Alekhine23/Chess-Robot/Solidworks Model/End Effector/end effector assembly.SLDASM

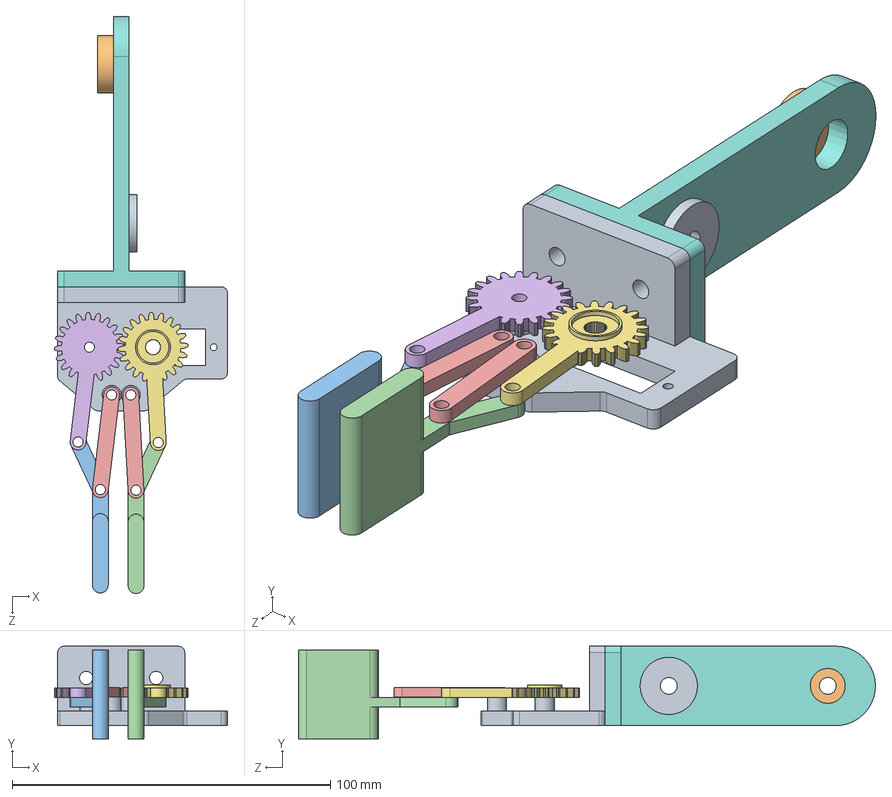
[picture p5: CAD file, 2025-10-30]
Solidworks Model/End Effector/end effector assembly.SLDASM
54.4 x 29.2 x 181.4 mm
chassis
chassis holder
splined grabber
unsplined grabber
link A x 2
link B
link C
standoff B
standoff A
