Alekhine23/Chess-Robot/Solidworks Model/End Effector/unsplined grabber.SLDPRT

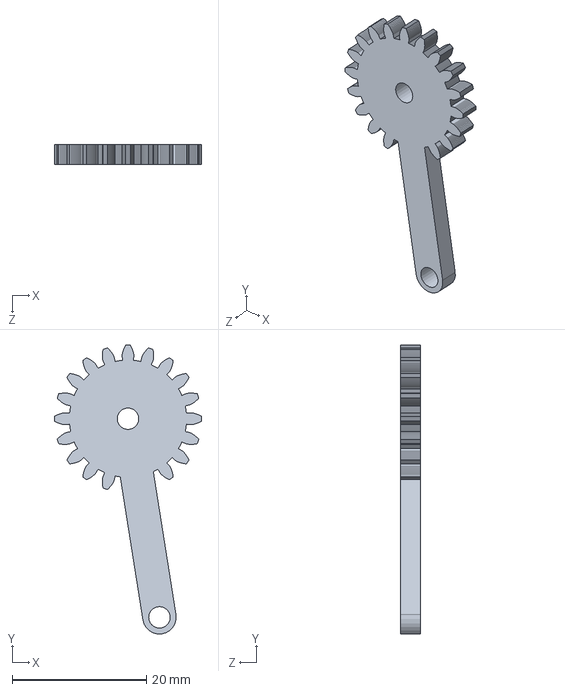
[picture p16: CAD file, 2025-10-30]
Solidworks Model/End Effector/unsplined grabber.SLDPRT
22.0 x 43.1 x 3.00 mm
