Alekhine23/Chess-Robot/STLs and dxfs/bottom base plate.DXF

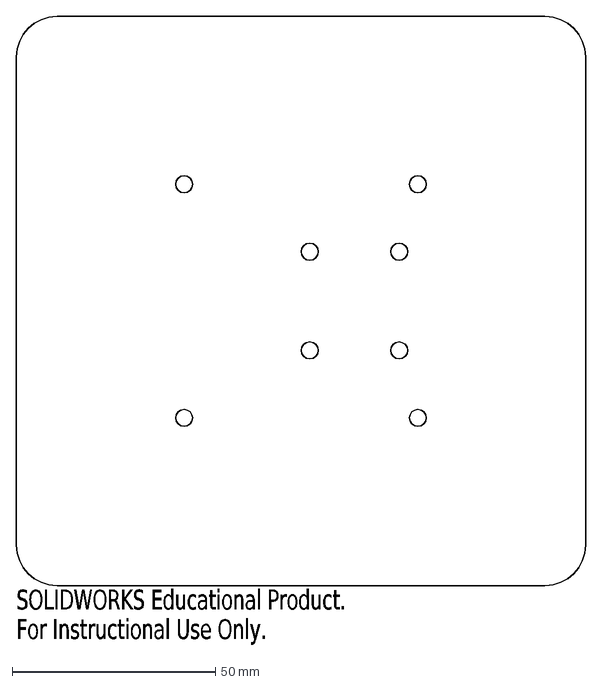
[picture p17: CAD file, 2025-10-30]
STLs and dxfs/bottom base plate.DXF
SOLIDWORKS Educational Product.
For Instructional Use Only.
