Alekhine23/Chess-Robot/Solidworks Model/End Effector/standoff A.SLDPRT

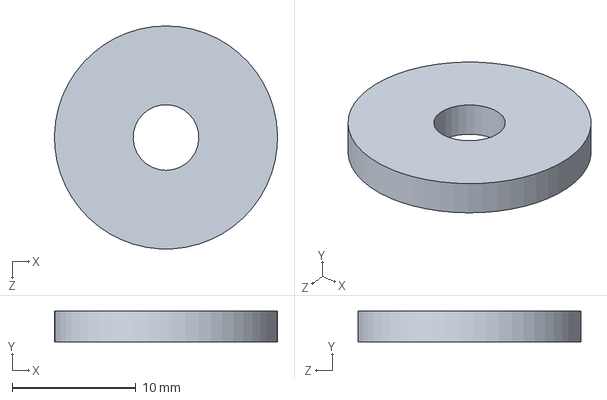
[picture p18: CAD file, 2025-10-30]
Solidworks Model/End Effector/standoff A.SLDPRT
18.0 x 2.50 x 18.0 mm
