Alekhine23/Chess-Robot/Solidworks Model/top base plate.SLDPRT

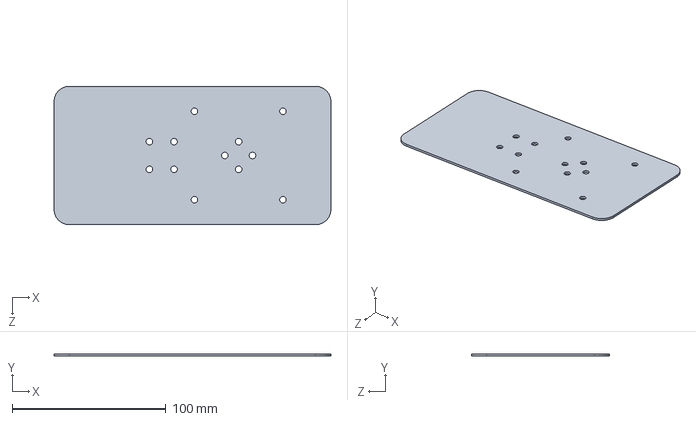
[picture p19: CAD file, 2025-10-30]
Solidworks Model/top base plate.SLDPRT
180.0 x 1.50 x 90.0 mm
