Alekhine23/Chess-Robot/STLs and dxfs/top base plate.DXF

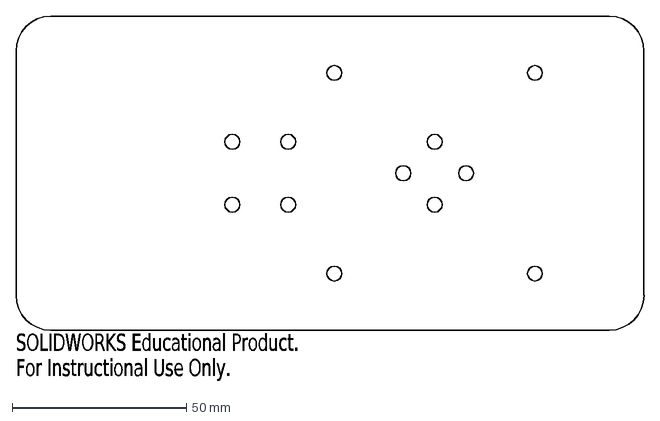
[picture p20: CAD file, 2025-10-30]
STLs and dxfs/top base plate.DXF
SOLIDWORKS Educational Product.
For Instructional Use Only.
