Alekhine23/Chess-Robot/Solidworks Model/pitch motor drive gear.SLDPRT

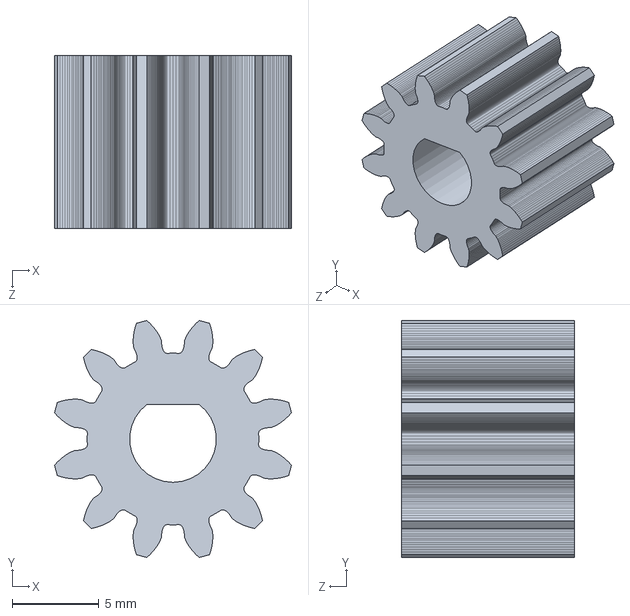
[picture p21: CAD file, 2025-10-30]
Solidworks Model/pitch motor drive gear.SLDPRT
13.7 x 13.7 x 10.0 mm
