Alekhine23/Chess-Robot/STLs and dxfs/shoulder elbow link 1A.STL

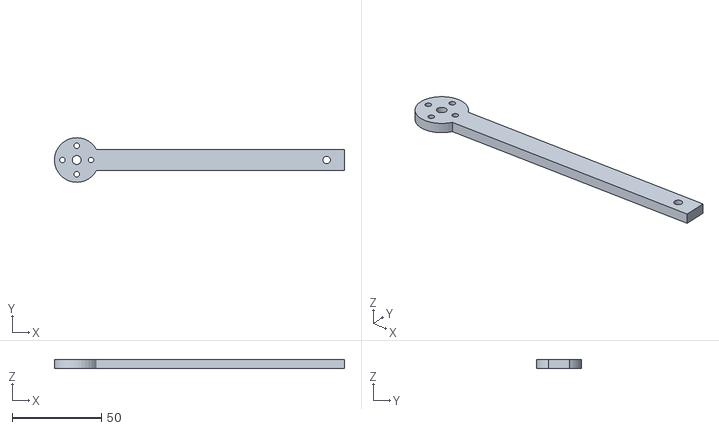
[picture p22: CAD file, 2025-10-30]
STLs and dxfs/shoulder elbow link 1A.STL
162.5 x 25.0 x 5.00
