Alekhine23/Chess-Robot/Solidworks Model/End Effector/standoff B.SLDPRT

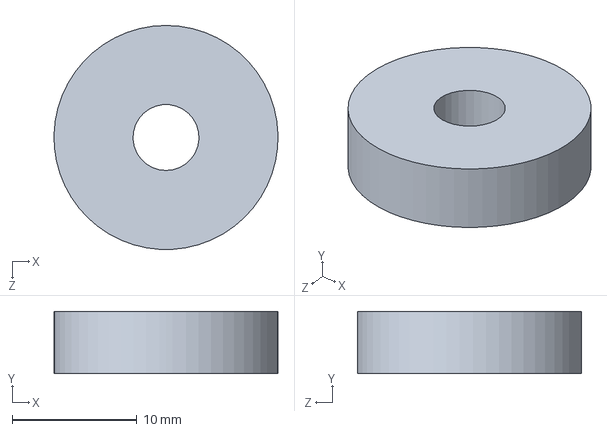
[picture p23: CAD file, 2025-10-30]
Solidworks Model/End Effector/standoff B.SLDPRT
18.0 x 5.00 x 18.0 mm
