Alekhine23/Chess-Robot/Solidworks Model/shoulder elbow link 4B.SLDPRT

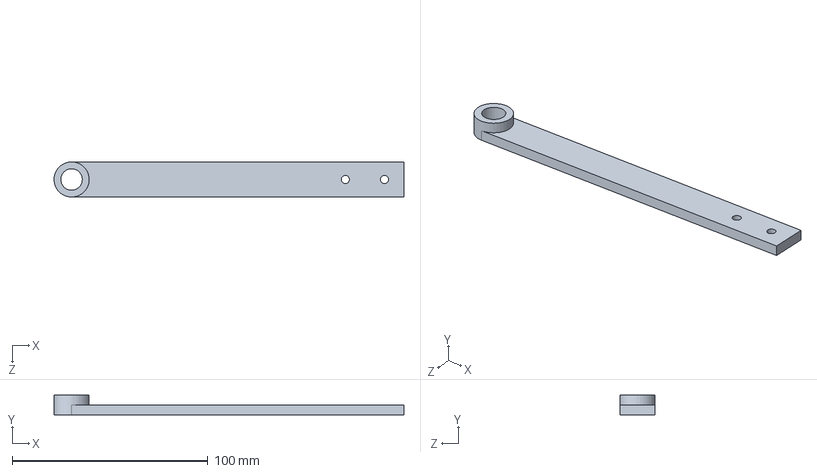
[picture p24: CAD file, 2025-10-30]
Solidworks Model/shoulder elbow link 4B.SLDPRT
179.0 x 10.0 x 18.0 mm
