Alekhine23/Chess-Robot/STLs and dxfs/shoulder elbow link 2B.STL

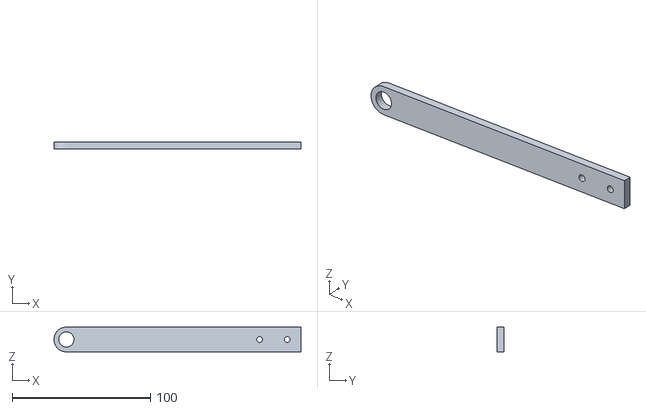
[picture p25: CAD file, 2025-10-30]
STLs and dxfs/shoulder elbow link 2B.STL
179.0 x 5.00 x 18.0
