Alekhine23/Chess-Robot/Solidworks Model/End Effector/link C.SLDPRT

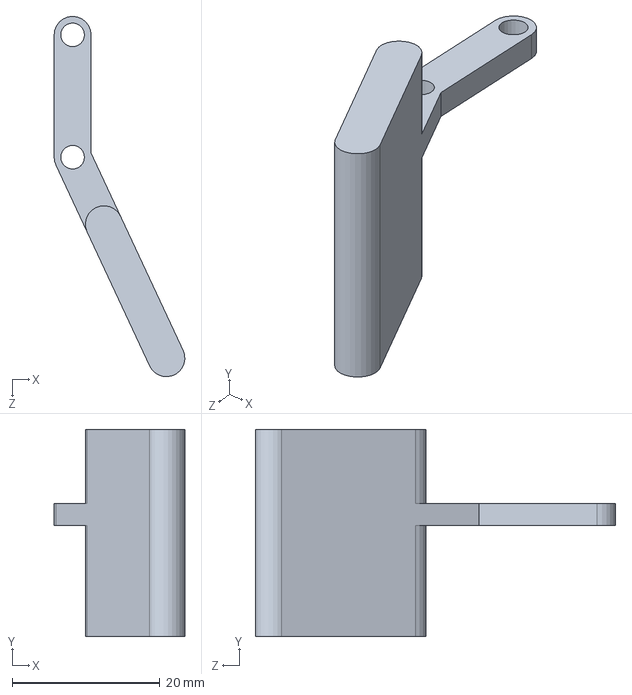
[picture p26: CAD file, 2025-10-30]
Solidworks Model/End Effector/link C.SLDPRT
17.7 x 28.0 x 48.7 mm
