Alekhine23/Chess-Robot/Solidworks Model/shoulder axle shaft collar.SLDPRT

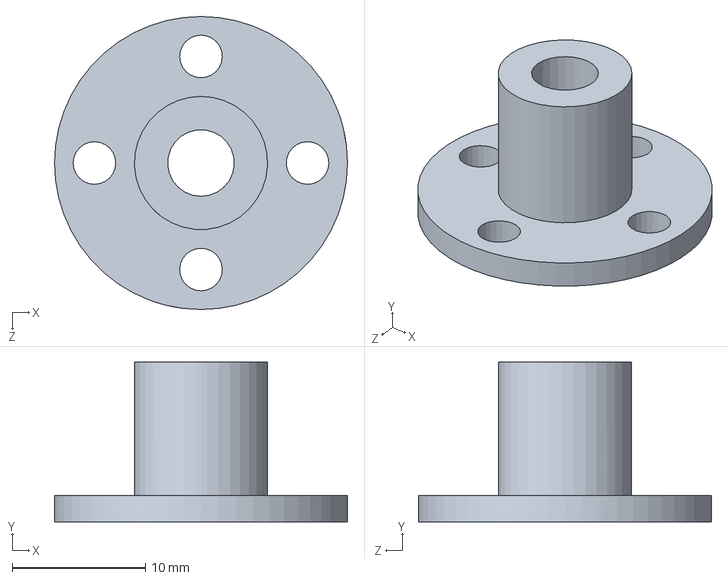
[picture p27: CAD file, 2025-10-30]
Solidworks Model/shoulder axle shaft collar.SLDPRT
22.0 x 12.0 x 22.0 mm
