Alekhine23/Chess-Robot/STLs and dxfs/chassis.STL

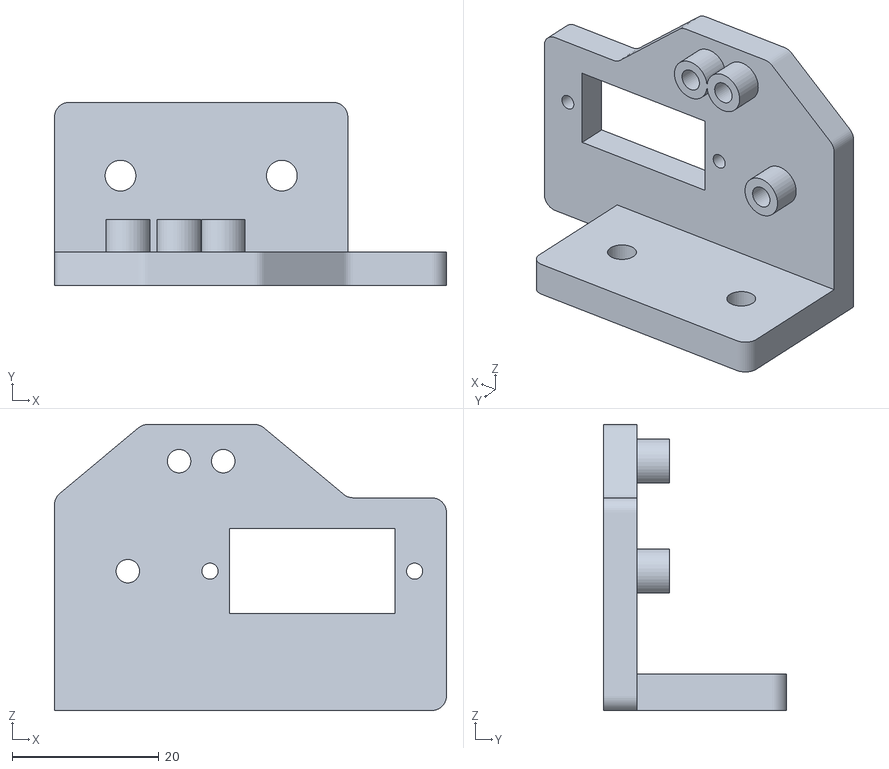
[picture p28: CAD file, 2025-10-30]
STLs and dxfs/chassis.STL
53.5 x 25.0 x 39.0
