Alekhine23/Chess-Robot/Solidworks Model/End Effector/chassis holder.SLDPRT

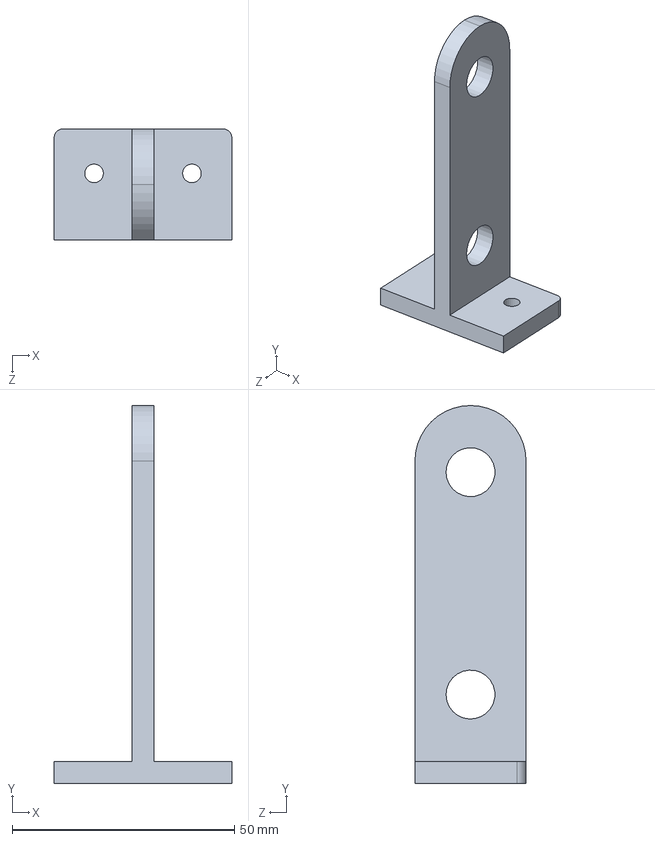
[picture p29: CAD file, 2025-10-30]
Solidworks Model/End Effector/chassis holder.SLDPRT
40.0 x 85.0 x 25.0 mm
