Alekhine23/Chess-Robot/Solidworks Model/shoulder middle axle support.SLDPRT

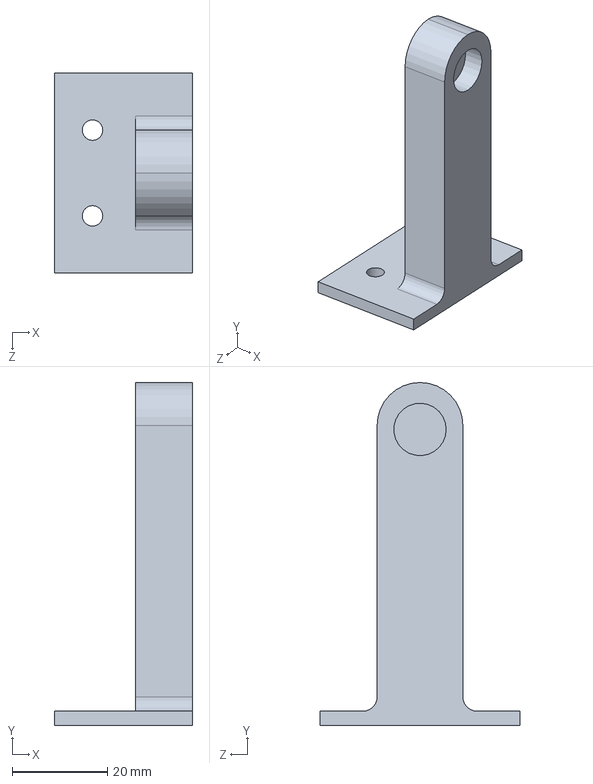
[picture p30: CAD file, 2025-10-30]
Solidworks Model/shoulder middle axle support.SLDPRT
29.0 x 72.0 x 42.0 mm
