Alekhine23/Chess-Robot/STLs and dxfs/yaw motor mount.STL

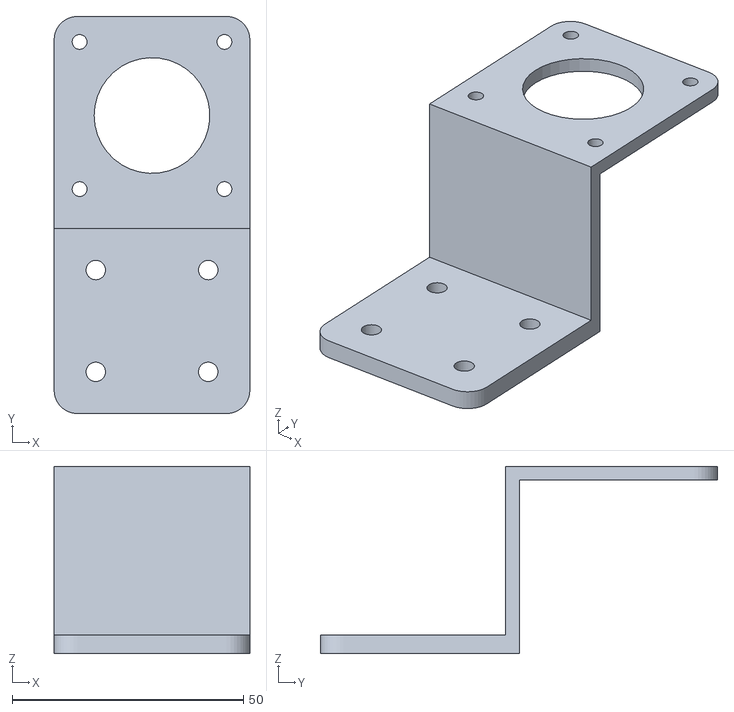
[picture p31: CAD file, 2025-10-30]
STLs and dxfs/yaw motor mount.STL
42.3 x 85.8 x 40.5
