Alekhine23/Chess-Robot/Solidworks Model/5dia 10 long shaft.SLDPRT

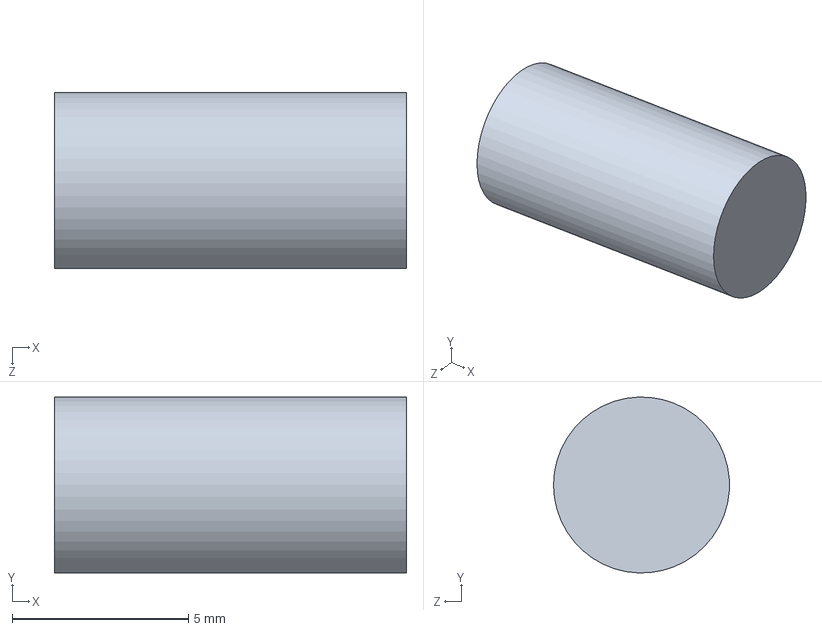
[picture p32: CAD file, 2025-10-30]
Solidworks Model/5dia 10 long shaft.SLDPRT
10.0 x 5.00 x 5.00 mm
