Alekhine23/Chess-Robot/Solidworks Model/5dia 25 long shaft.SLDPRT

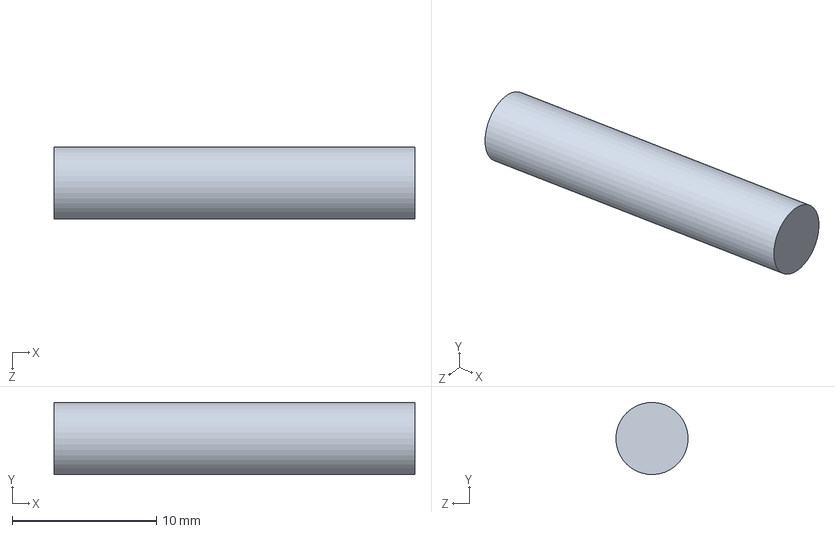
[picture p33: CAD file, 2025-10-30]
Solidworks Model/5dia 25 long shaft.SLDPRT
25.0 x 5.00 x 5.00 mm
