Alekhine23/Chess-Robot/Solidworks Model/pitch motor driven gear.SLDPRT

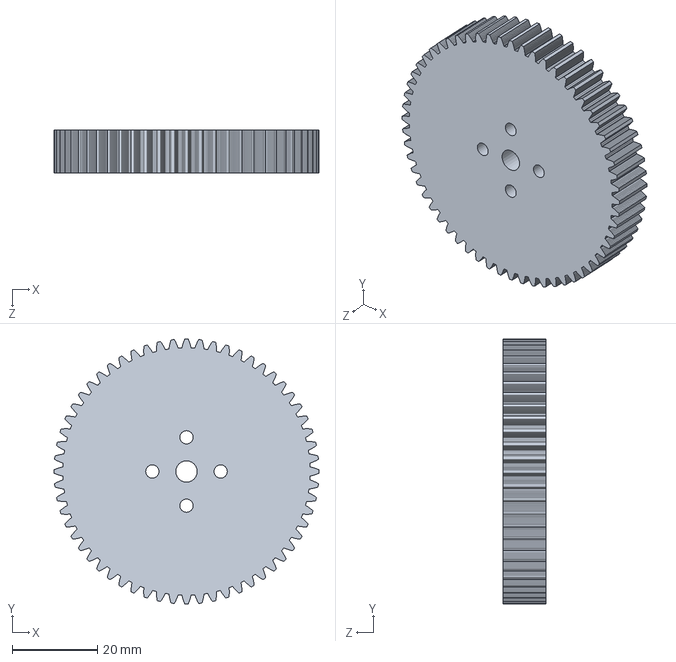
[picture p34: CAD file, 2025-10-30]
Solidworks Model/pitch motor driven gear.SLDPRT
62.0 x 62.0 x 10.0 mm
