Alekhine23/Chess-Robot/STLs and dxfs/shoulder elbow link 1B.STL

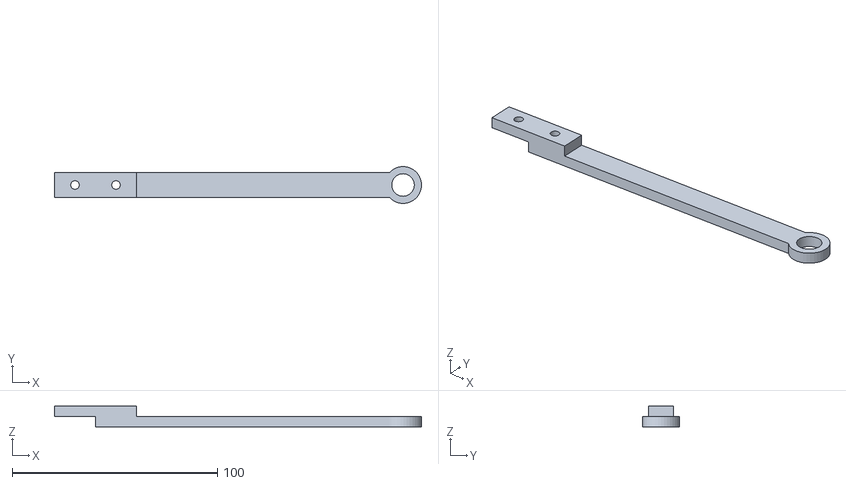
[picture p35: CAD file, 2025-10-30]
STLs and dxfs/shoulder elbow link 1B.STL
179.0 x 18.0 x 10.0
