Alekhine23/Chess-Robot/Solidworks Model/yaw motor driven gear.SLDPRT

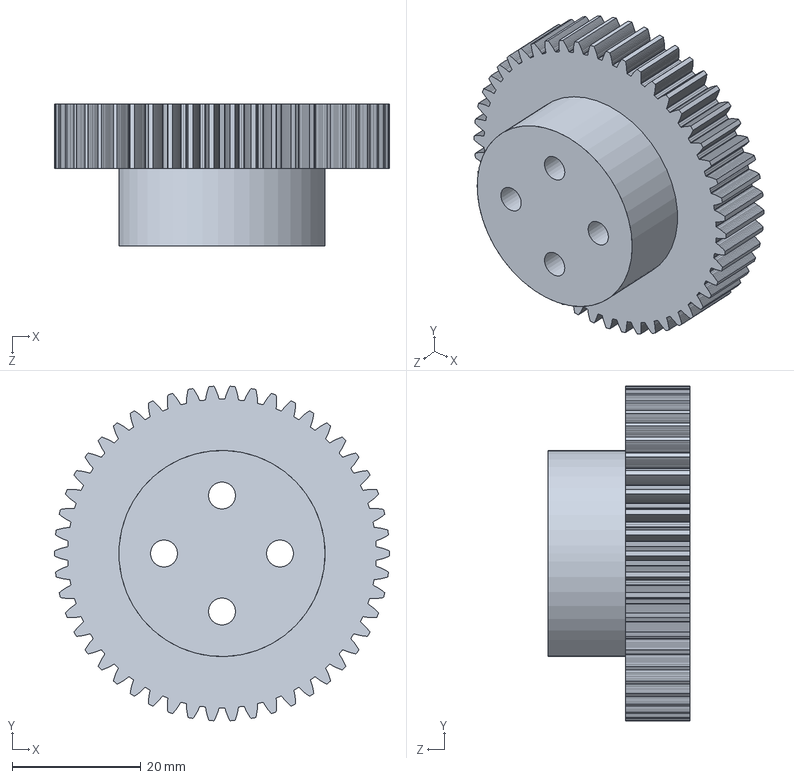
[picture p36: CAD file, 2025-10-30]
Solidworks Model/yaw motor driven gear.SLDPRT
52.0 x 51.9 x 22.0 mm
