Alekhine23/Chess-Robot/Solidworks Model/5dia 15 long shaft.SLDPRT

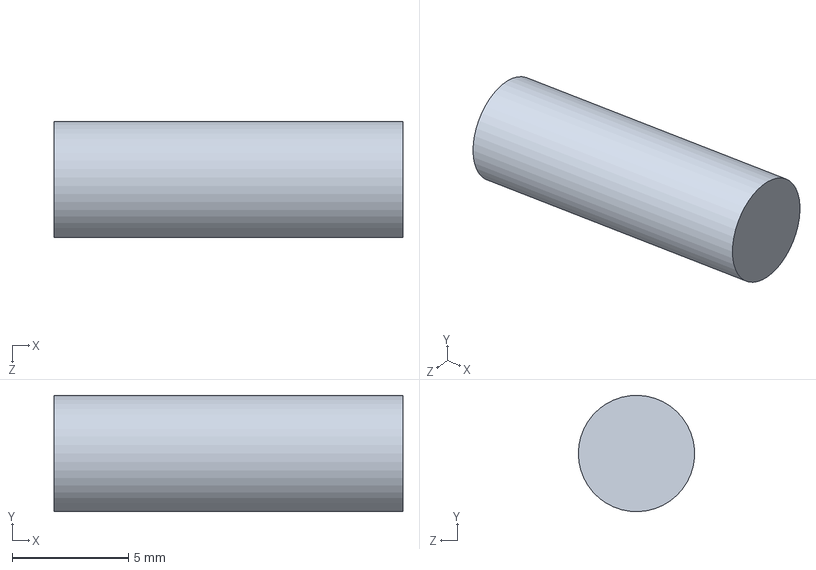
[picture p37: CAD file, 2025-10-30]
Solidworks Model/5dia 15 long shaft.SLDPRT
15.0 x 5.00 x 5.00 mm
