Alekhine23/Chess-Robot/Solidworks Model/pitch motor mount B.SLDPRT

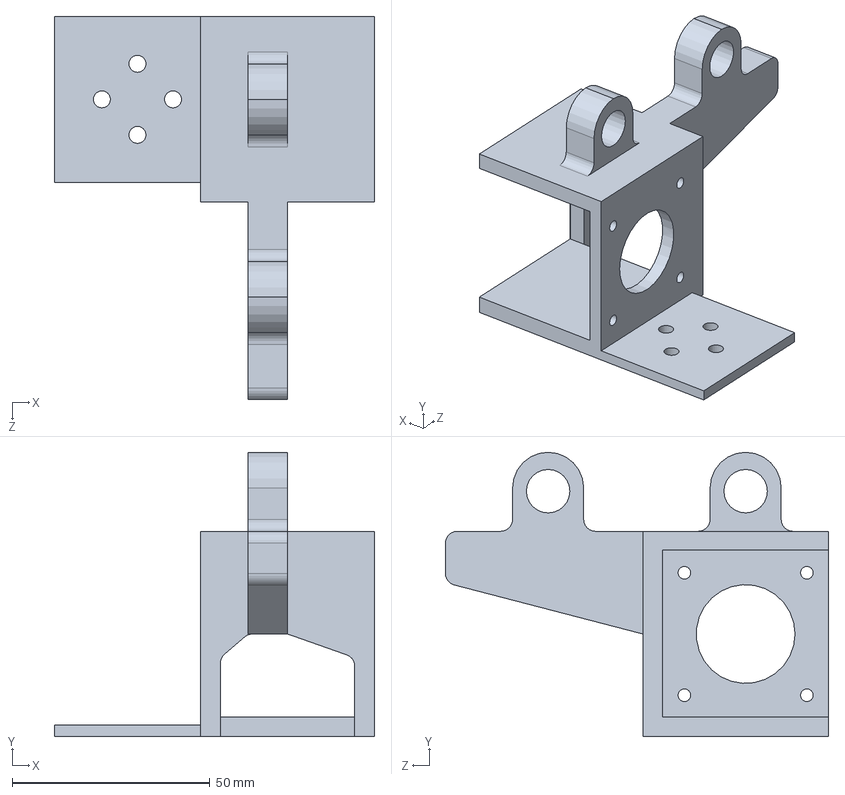
[picture p38: CAD file, 2025-10-30]
Solidworks Model/pitch motor mount B.SLDPRT
81.0 x 72.0 x 97.0 mm
