Alekhine23/Chess-Robot/STLs and dxfs/elbow triangle link.STL

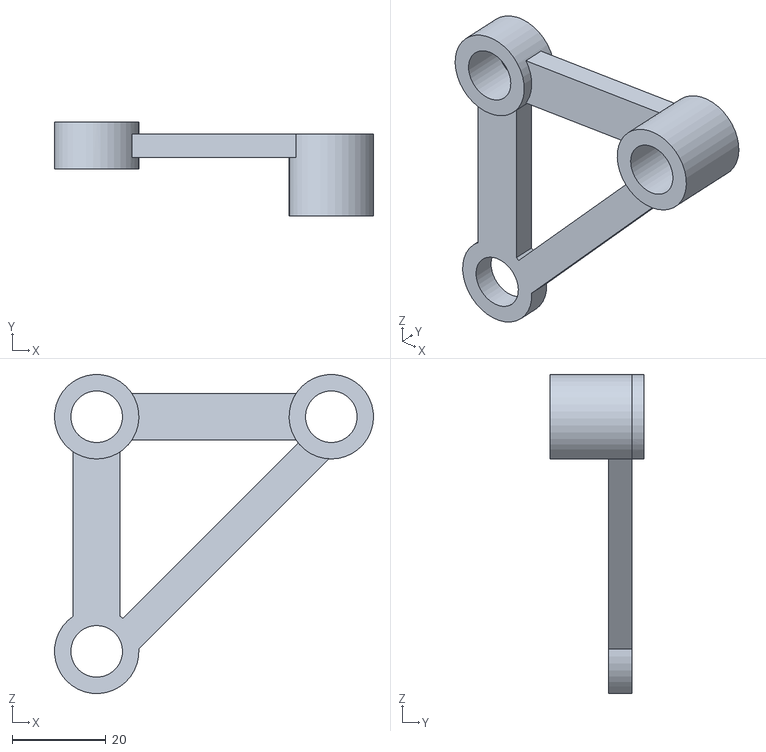
[picture p39: CAD file, 2025-10-30]
STLs and dxfs/elbow triangle link.STL
68.0 x 20.0 x 68.0
