Alekhine23/Chess-Robot/Solidworks Model/pitch motor mount A.SLDPRT

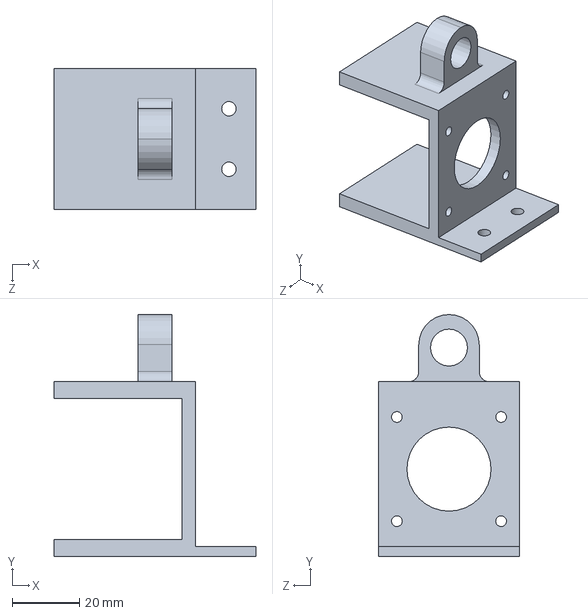
[picture p40: CAD file, 2025-10-30]
Solidworks Model/pitch motor mount A.SLDPRT
60.0 x 72.0 x 42.0 mm
