Alekhine23/Chess-Robot/Solidworks Model/5dia 20 long shaft.SLDPRT

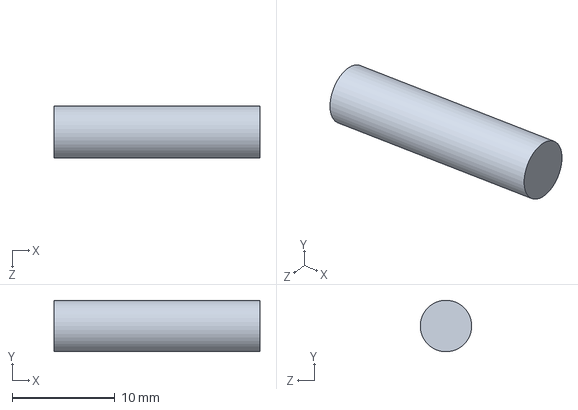
[picture p41: CAD file, 2025-10-30]
Solidworks Model/5dia 20 long shaft.SLDPRT
20.0 x 5.00 x 5.00 mm
