Alekhine23/Chess-Robot/Solidworks Model/5dia 22.5 long shaft.SLDPRT

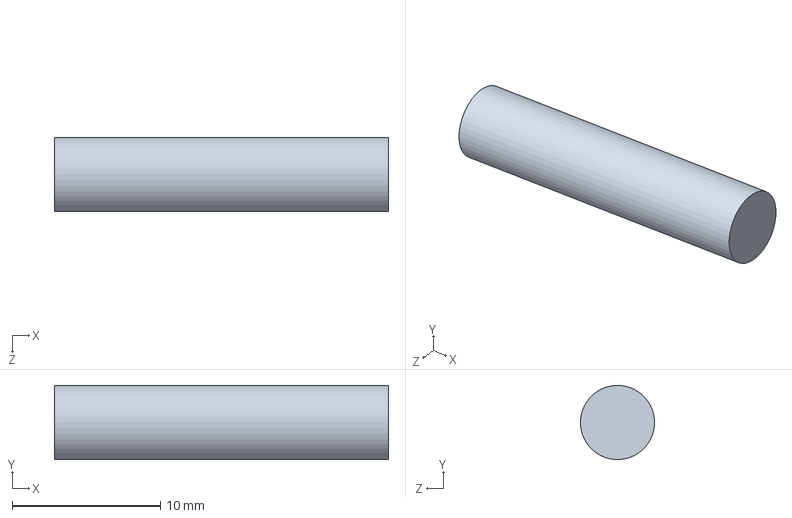
[picture p42: CAD file, 2025-10-30]
Solidworks Model/5dia 22.5 long shaft.SLDPRT
22.5 x 5.00 x 5.00 mm
