Alekhine23/Chess-Robot/Solidworks Model/board.SLDPRT

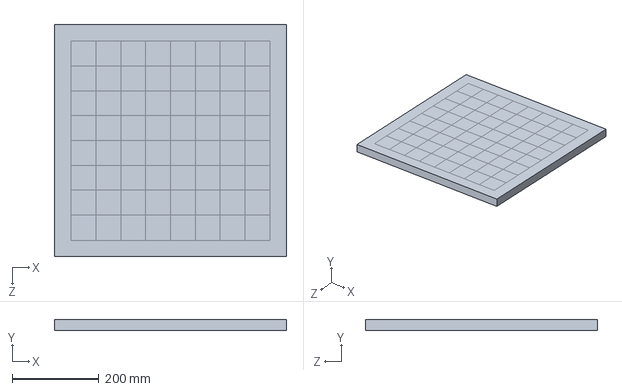
[picture p43: CAD file, 2025-10-30]
Solidworks Model/board.SLDPRT
533.4 x 25.4 x 533.4 mm
