Alekhine23/Chess-Robot/Solidworks Model/lazy susan bearing.SLDPRT

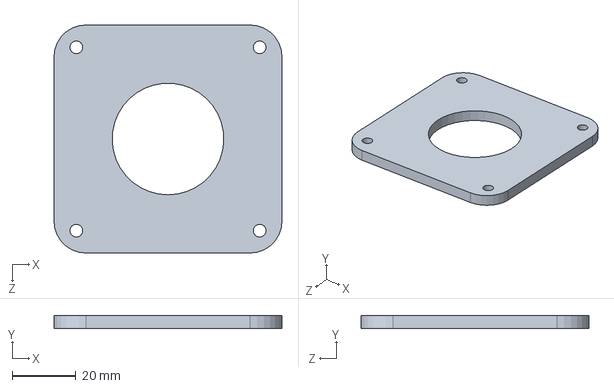
[picture p44: CAD file, 2025-10-30]
Solidworks Model/lazy susan bearing.SLDPRT
71.5 x 4.20 x 71.5 mm
