Alekhine23/Chess-Robot/Solidworks Model/base standoff.SLDPRT

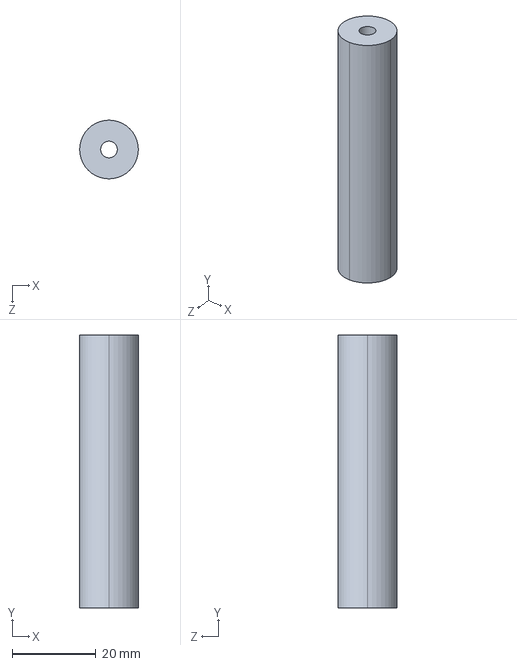
[picture p45: CAD file, 2025-10-30]
Solidworks Model/base standoff.SLDPRT
14.0 x 65.1 x 14.0 mm
