Alekhine23/Chess-Robot/Solidworks Model/5dia 59 long shaft.SLDPRT

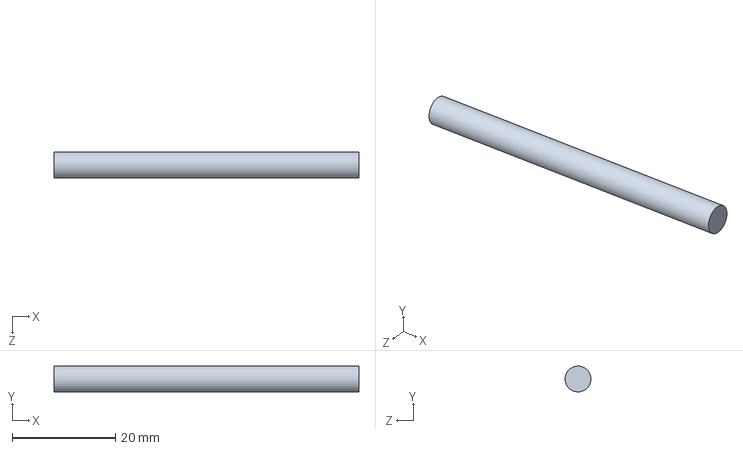
[picture p46: CAD file, 2025-10-30]
Solidworks Model/5dia 59 long shaft.SLDPRT
59.0 x 4.99 x 5.00 mm
