Alekhine23/Chess-Robot/STLs and dxfs/shoulder link 3.STL

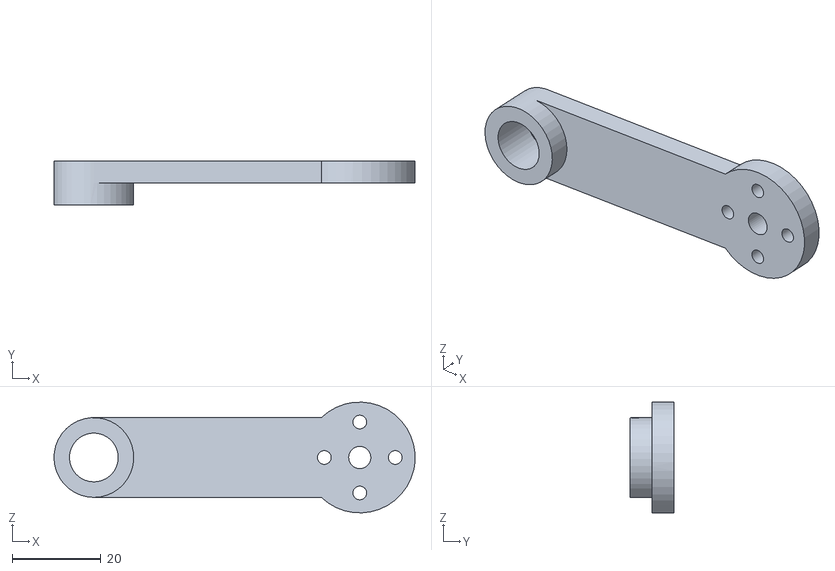
[picture p47: CAD file, 2025-10-30]
STLs and dxfs/shoulder link 3.STL
81.5 x 10.0 x 25.0
