Alekhine23/Chess-Robot/Solidworks Model/bottom base plate.SLDPRT

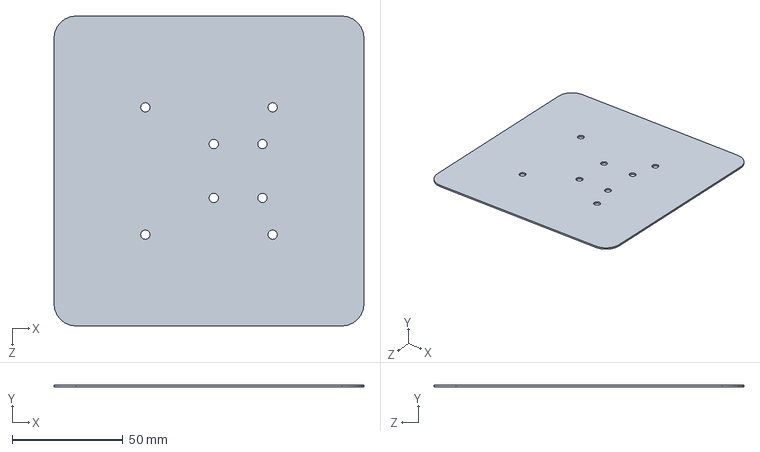
[picture p48: CAD file, 2025-10-30]
Solidworks Model/bottom base plate.SLDPRT
140.0 x 1.00 x 140.0 mm
