Alekhine23/Chess-Robot/Solidworks Model/5dia 40 long shaft.SLDPRT

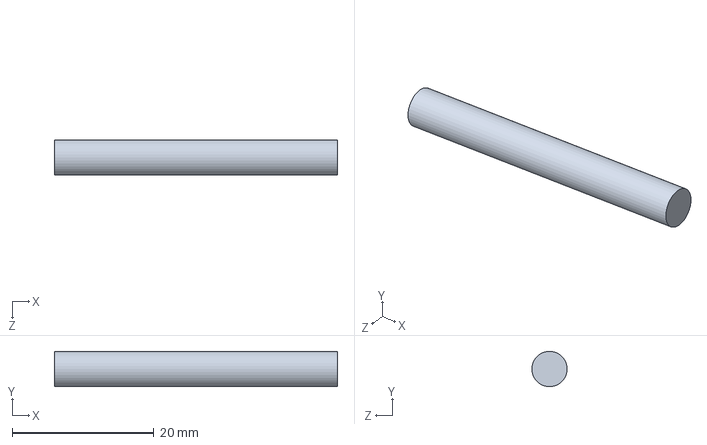
[picture p49: CAD file, 2025-10-30]
Solidworks Model/5dia 40 long shaft.SLDPRT
40.0 x 5.00 x 5.00 mm
