Alekhine23/Chess-Robot/Solidworks Model/5dia 28 long shaft.SLDPRT

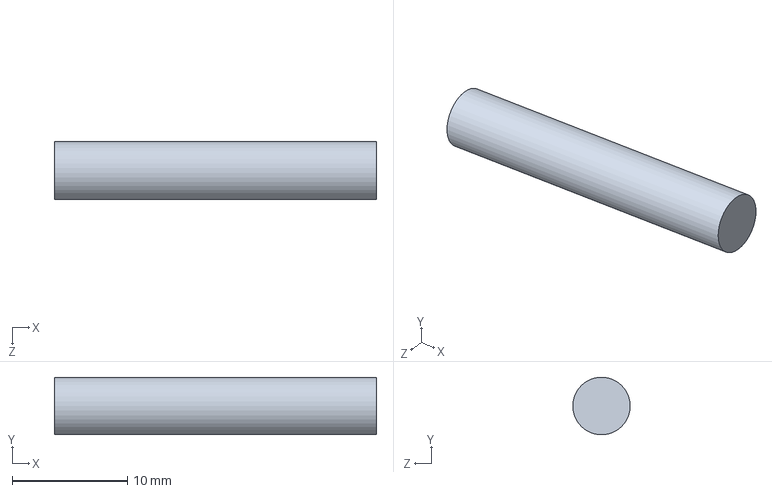
[picture p50: CAD file, 2025-10-30]
Solidworks Model/5dia 28 long shaft.SLDPRT
28.0 x 4.98 x 5.00 mm
