Alekhine23/Chess-Robot/Solidworks Model/5dia 12.5 long shaft.SLDPRT

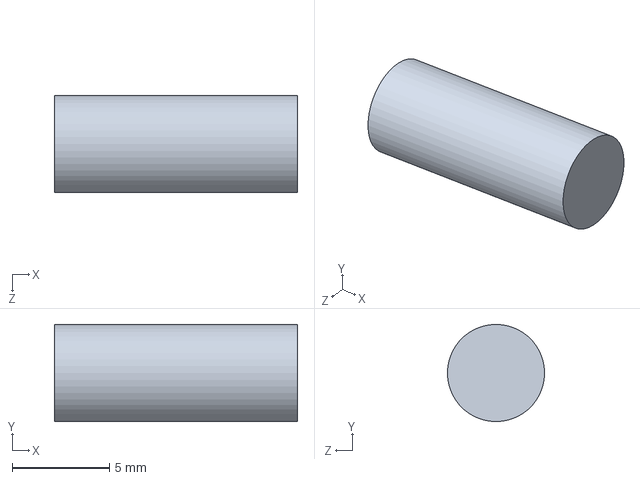
[picture p52: CAD file, 2025-10-30]
Solidworks Model/5dia 12.5 long shaft.SLDPRT
12.5 x 5.00 x 5.00 mm
